orpaltech/aapi/hardware/images/EV2400/PXL_20260128_093411728.jpg

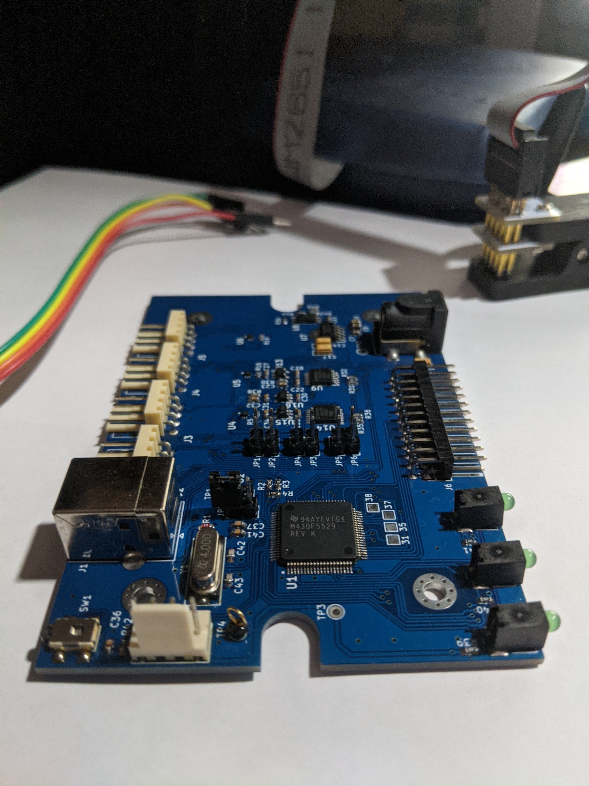
hardware/images/EV2400/PXL_20260128_093411728.jpg
