orpaltech/aapi/hardware/images/EV2400/PXL_20260128_093420092.jpg

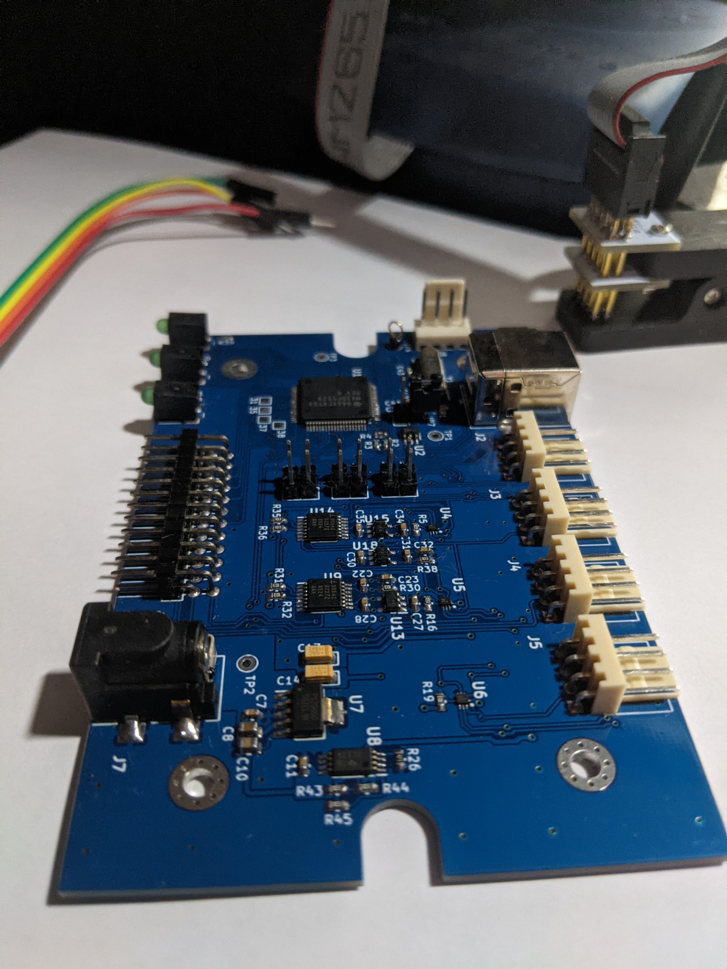
hardware/images/EV2400/PXL_20260128_093420092.jpg
