orpaltech/aapi/hardware/images/v4.2/PXL_20260226_131348575.jpg

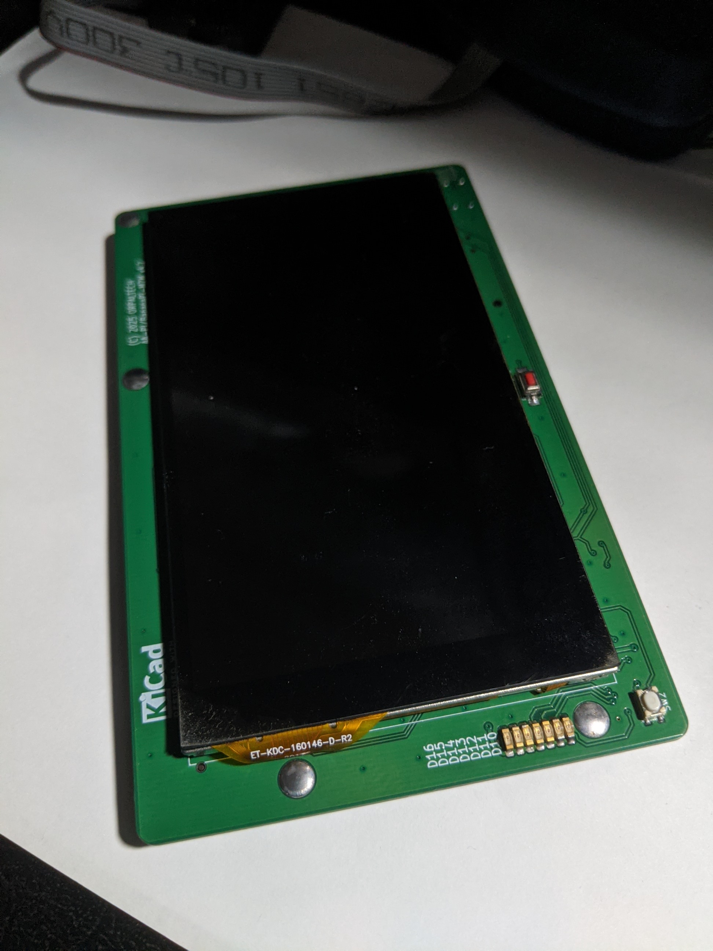
hardware/images/v4.2/PXL_20260226_131348575.jpg
