orpaltech/aapi/hardware/images/v4.2/PXL_20260226_131544818.jpg

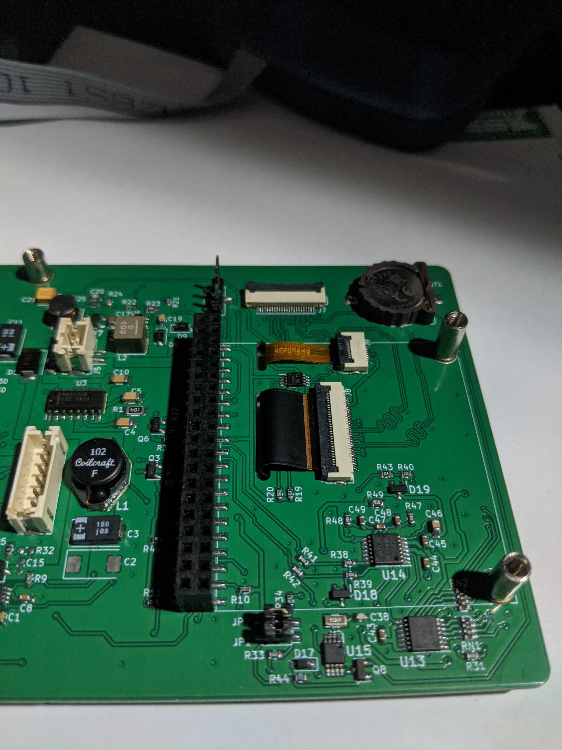
hardware/images/v4.2/PXL_20260226_131544818.jpg
