orpaltech/aapi/hardware/images/v4.2/PXL_20260226_131830843.jpg

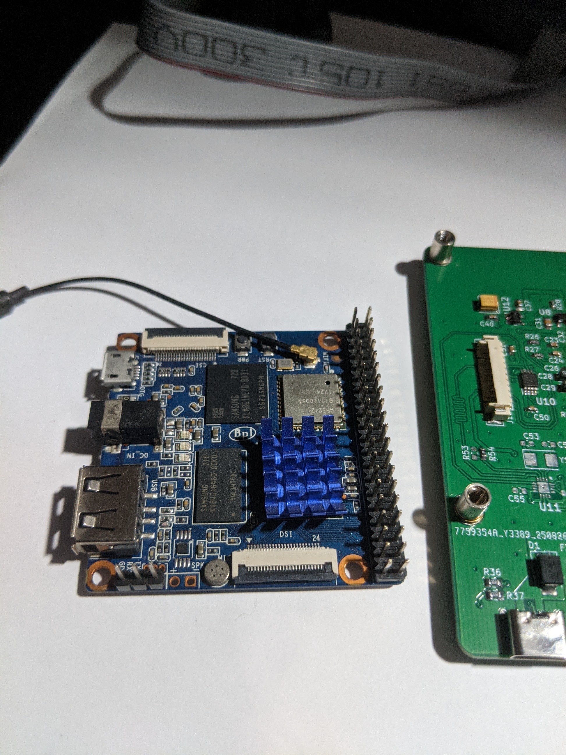
hardware/images/v4.2/PXL_20260226_131830843.jpg
