orpaltech/aapi/antenna-analyzer/src/app/ui/aapi_configuration_view.h

/*
 * This file is part of the ORPALTECH AA-PI project
 *  (https://github.com/orpaltech/aapi).
 *
 * Copyright (c) 2013-2026 ORPAL Technology, Inc.
 *
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
 * You should have received a copy of the GNU General Public License
 * along with this program. If not, see <http://www.gnu.org/licenses/>.
 */

#ifndef UI_AAPI_CONFIGURATION_VIEW_H
#define UI_AAPI_CONFIGURATION_VIEW_H

#include "aapi_view_backend.h"

///////////////////////////////////////////////////////////////////////////////
// class QAAPiConfigurationView
///////////////////////////////////////////////////////////////////////////////

class QAAPiConfigurationView : public QAAPiViewBackend
{
public:
    enum ConfigParamType {
        PT_BYTE = (uint)AAPiVariantType::BYTE,
        PT_UINT = (uint)AAPiVariantType::UINT,
        PT_INT = (uint)AAPiVariantType::INT,
        PT_FLOAT = (uint)AAPiVariantType::FLOAT,
        PT_TEXT = (uint)AAPiVariantType::TEXT
    };

    Q_OBJECT
    QML_UNCREATABLE(AAPI_QML_UNCREATABLE_REASON)
    QML_NAMED_ELEMENT(ConfigurationViewBackend)

    /* Enumerations */
    Q_ENUM(ConfigParamType)

    /* Properties */
    Q_PROPERTY(uint num_params READ get_num_params NOTIFY raiseNumParamsChanged)
    Q_PROPERTY(uint param_index READ get_param_index)
    Q_PROPERTY(uint param_num_options READ get_num_options NOTIFY raiseNumOptionsChanged)
    Q_PROPERTY(QStringList param_opt_values READ get_opt_values)
    Q_PROPERTY(QStringList param_opt_labels READ get_opt_labels)
    Q_PROPERTY(QString param_description READ get_description)
    Q_PROPERTY(ConfigParamType param_type READ get_type)
    Q_PROPERTY(QString param_value READ get_value)
    Q_PROPERTY(bool is_dirty_config READ is_dirty_config)

public:
    explicit QAAPiConfigurationView(AAPiConfig *config, QObject *parent = Q_NULLPTR);
    ~QAAPiConfigurationView();

    /* Property accessors */
    uint32_t get_num_params() const;
    int get_param_index() const { return m_index;}
    uint32_t get_num_options() const;
    QStringList get_opt_values() const;
    QStringList get_opt_labels() const;
    QString get_description() const;
    QString get_value() const;
    bool is_dirty_config() const;
    ConfigParamType get_type() const;

private:
// QAAPiViewBackend
    AAPiError onViewLoad() override;
    void onViewDestroy() override;

    QString formatValue(const AAPiVariant& value) const;

private:
    AAPiPtr<AAPiConfig> m_tmpConfig;
    int m_index;

Q_SIGNALS:
    void raiseNumParamsChanged();
    void raiseNumOptionsChanged();

public Q_SLOTS:
    void handleMovePrevParam();
    void handleMoveNextParam();
    void handleMoveFirstParam();
    void handleSetParamValue(QString new_val);
    void handleSetParamOption(int new_opt);
    void handleUseDefaults();
    void handleAcceptChanges();
    void handleDiscardChanges();
};

#endif // UI_AAPI_CONFIGURATION_VIEW_H
