orpaltech/aapi/antenna-analyzer/src/app/ui/aapi_about_app_view.cpp

/*
 * This file is part of the ORPALTECH AA-PI project
 *  (https://github.com/orpaltech/aapi).
 *
 * Copyright (c) 2013-2025 ORPAL Technology, Inc.
 *
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
 * You should have received a copy of the GNU General Public License
 * along with this program. If not, see <http://www.gnu.org/licenses/>.
 */

#include <QApplication>
#include <QProcess>
#include <QScreen>
#include <QSysInfo>
#include <QStorageInfo>
#include "aapi_about_app_view.h"
#include "aapi_application.h"


///////////////////////////////////////////////////////////////////////////////
// class QAAPiAboutAppView
///////////////////////////////////////////////////////////////////////////////

QAAPiAboutAppView::QAAPiAboutAppView(AAPiConfig *config, QObject *parent)
    : QAAPiViewBackend(config, nullptr, nullptr, nullptr, parent)
{
}

void QAAPiAboutAppView::handleQuit()
{
    emit quitApplication();
}

void QAAPiAboutAppView::handleReboot()
{
    emit rebootApplication();
}

QString QAAPiAboutAppView::getSystemInformation() const
{
    QString text;

    QString memInfo;
    QProcess p;
    p.start("awk", QStringList() << "/MemAvailable/ { print $2 }" << "/proc/meminfo");
    p.waitForFinished();
    memInfo = QString::number(p.readAllStandardOutput().toUInt() / 1024) + "MB / ";
    p.close();
    p.start("awk", QStringList() << "/MemTotal/ { print $2 }" << "/proc/meminfo");
    p.waitForFinished();
    memInfo += QString::number(p.readAllStandardOutput().toUInt() / 1024) + "MB";
    p.close();

    QStorageInfo stg = QStorageInfo::root();
    QString diskInfo = stg.fileSystemType() + " | " + QString::number(stg.bytesAvailable()/1000/1000) + "MB / " + QString::number(stg.bytesTotal()/1000/1000) + "MB";

    QScreen *scr = QApplication::primaryScreen();
    QString scrInfo = scr->name() + " | ";
    scrInfo += QString::number(scr->availableSize().width()) + "x" + QString::number(scr->availableSize().height()) + "@";
    scrInfo += QVariant(scr->refreshRate()).toString() + "Hz | ";
    scrInfo += QString::number(scr->physicalDotsPerInch(), 'f', 2) + "dpi";

    QAAPiApplication *aapi = qobject_cast<QAAPiApplication *>(parent( ));

    text =  "System:\t" + QSysInfo::prettyProductName() + "\n" +
            "Kernel:\t" + QSysInfo::kernelVersion() + "\n" +
            "CPU:   \t" + QSysInfo::buildCpuArchitecture() + " | " + QSysInfo::buildAbi() + "\n" +
            "GPU:   \t" + aapi->getGraphicsDeviceInfo() + "\n" +
            "RAM:   \t" + memInfo + "\n" +
            "Disk:  \t" + diskInfo + "\n" +
            "Screen:\t" + scrInfo;

    return text;
}
